ankelefs/point-welder/POINT-WELDER-V2/HARDWARE/Point-Welder-V2-Schematics.sch

## EAGLE design POINT-WELDER-V2/HARDWARE/Point-Welder-V2-Schematics.sch (2022-12-30)

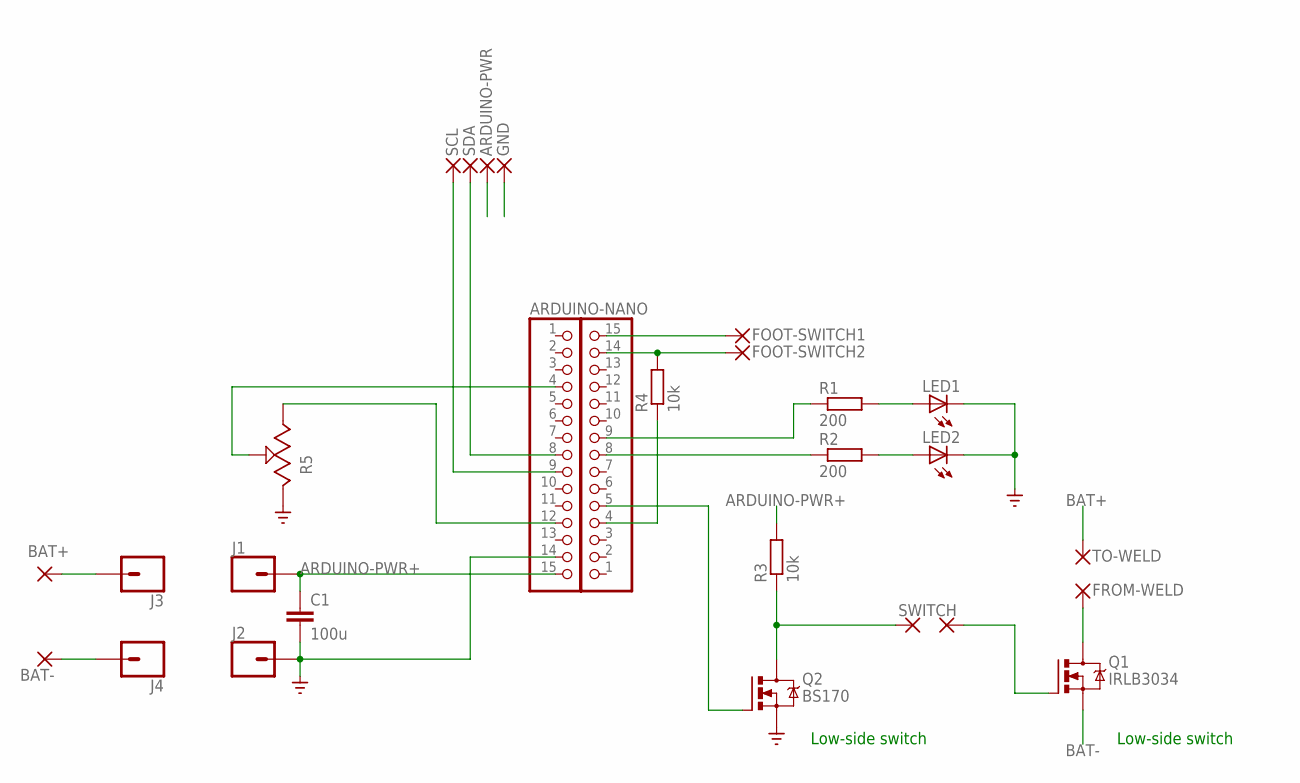
[picture p7: schematic Point-Welder-V2-Schematics.sch]

Parts:
ARDUINO-NANO: PINHD-1X15; 1X15
ARDUINO-PWR: SMD2; SMD1,27-2,54
BAT-: SMD5; SMD2,54-5,08
C1: 100u; C025-060X050
FOOT-SWITCH1, FOOT-SWITCH2: SMD2; SMD1,27-2,54
FROM-WELD: SMD5; SMD2,54-5,08
GND: SMD2; SMD1,27-2,54
J1, J2, J3, J4: CONN_01; 1X01
JP1: PINHD-1X15; 1X15
LED1, LED2: LED3MM
PAD3: SMD2; SMD1,27-2,54
PAD11: SMD5; SMD2,54-5,08
Q1: IRLB3034; TO220BV; MPN IRLB3034PBF
Q2: BS170; TO92
R1, R2: 200; 0204/7
R3, R4: 10k; 0204/7
R5: 91A1A-B28-B15L; 91A1A-B28-B15L-ND
SCL: SMD2; SMD1,27-2,54
SDA: SMD2; SMD1,27-2,54
SWITCH: SMD2; SMD1,27-2,54
TO-WELD: SMD5; SMD2,54-5,08

Connections:
ARDUINO-PWR+: ARDUINO-NANO.15, ARDUINO-PWR.1, C1.1, J1.1, R3.2
BAT+: J3.1, PAD11.1, TO-WELD.1
BAT-: BAT-.1, J4.1, Q1.S
DRIVER: JP1.5, Q2.2 (G)
FOOT-SWITCH+: FOOT-SWITCH1.1, JP1.15
FOOT-SWITCH-: FOOT-SWITCH2.1, JP1.14, R4.2
GND: ARDUINO-NANO.14, C1.2, GND.1, J2.1, LED1.K (C), LED2.K (C), Q2.3 (S), R5.1
unnamed: Q2.1 (D), R3.1, SWITCH.1
unnamed: LED2.A, R2.2
unnamed: LED1.A, R1.2
unnamed: ARDUINO-NANO.4, R5.2
unnamed: JP1.4, R4.1
unnamed: PAD3.1, Q1.G
unnamed: JP1.9, R1.1
unnamed: JP1.8, R2.1
unnamed: ARDUINO-NANO.12, R5.3
unnamed: ARDUINO-NANO.9, SCL.1
unnamed: ARDUINO-NANO.8, SDA.1
unnamed: FROM-WELD.1, Q1.D

Notes on the sheet:
Low-side switch
